alepetri/trap_camera/CAD/Pi/raspberry_pi_B+_(audio_video2).SLDPRT

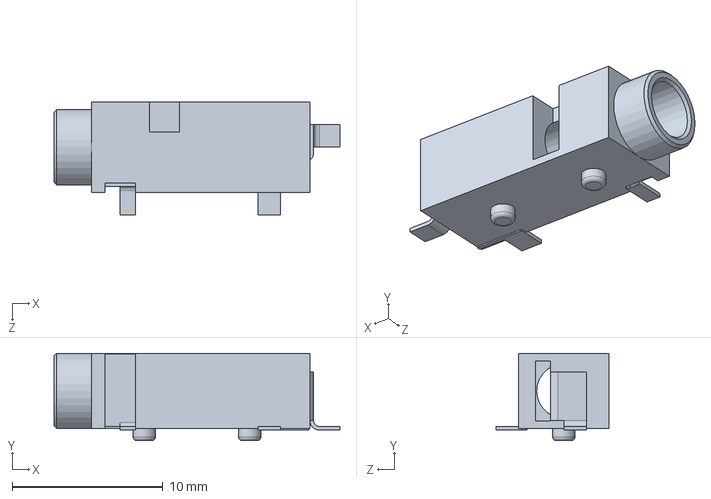
[picture p16: CAD file, 2021-12-30]
CAD/Pi/raspberry_pi_B+_(audio_video2).SLDPRT
19.0 x 5.80 x 7.50 mm
