alepetri/trap_camera/CAD/Trap_Camera_Lid.SLDPRT

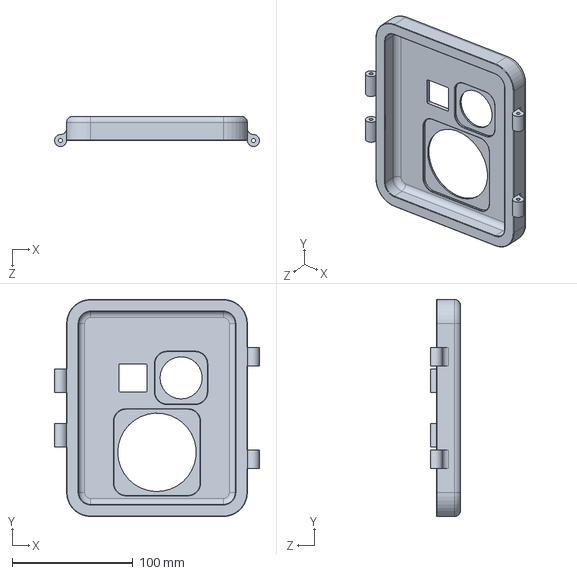
[picture p17: CAD file, 2021-12-30]
CAD/Trap_Camera_Lid.SLDPRT
170.0 x 180.0 x 25.0 mm
