alepetri/trap_camera/CAD/Pi/raspberry_pi_B+_(micro_USB_cover).SLDPRT

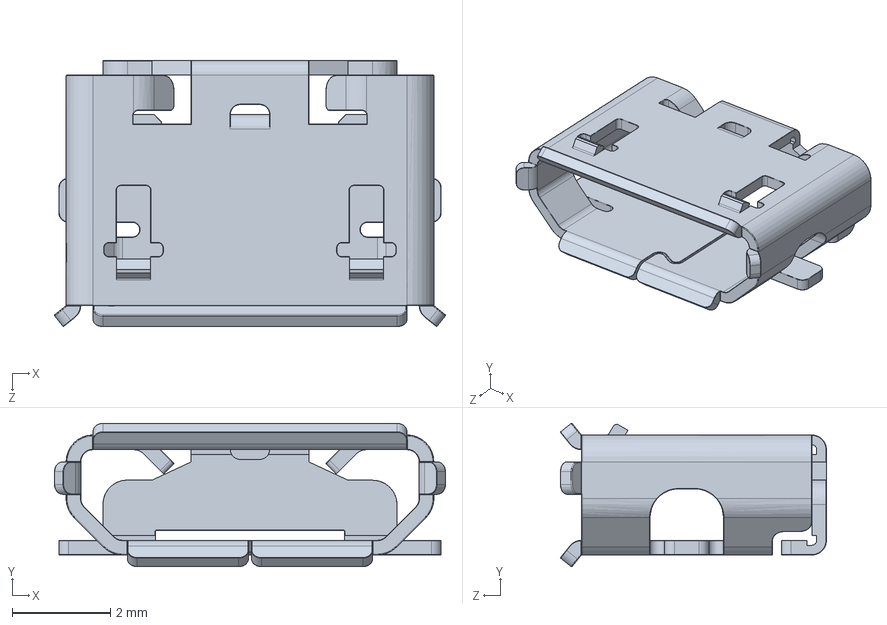
[picture p18: CAD file, 2021-12-30]
CAD/Pi/raspberry_pi_B+_(micro_USB_cover).SLDPRT
7.97 x 2.92 x 5.43 mm
