alepetri/trap_camera/CAD/test.STL

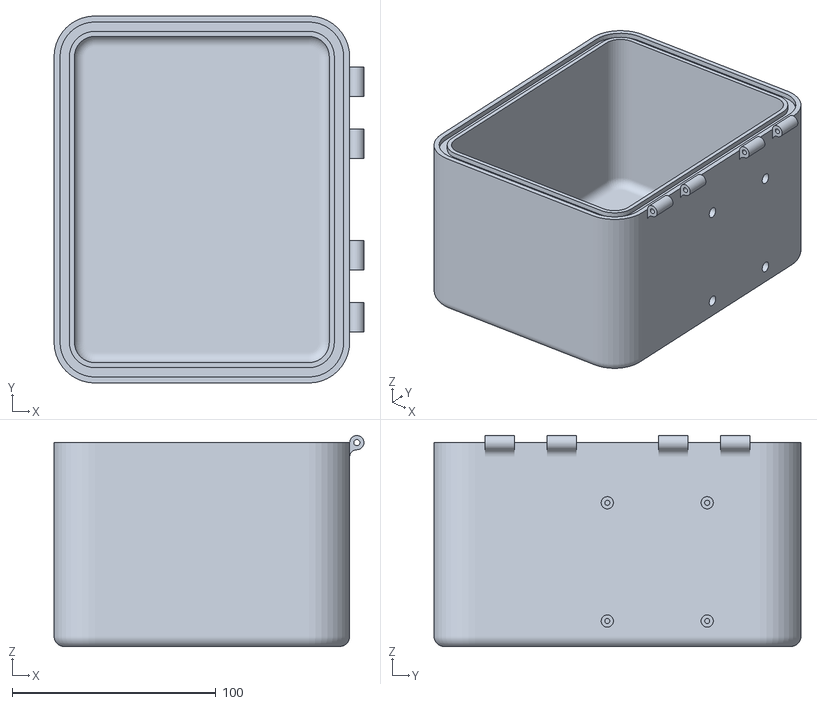
[picture p19: CAD file, 2021-12-30]
CAD/test.STL
152.0 x 180.0 x 103.5
