alepetri/trap_camera/CAD/Pi/raspberry_pi_B+_(microsd_slot2).SLDPRT

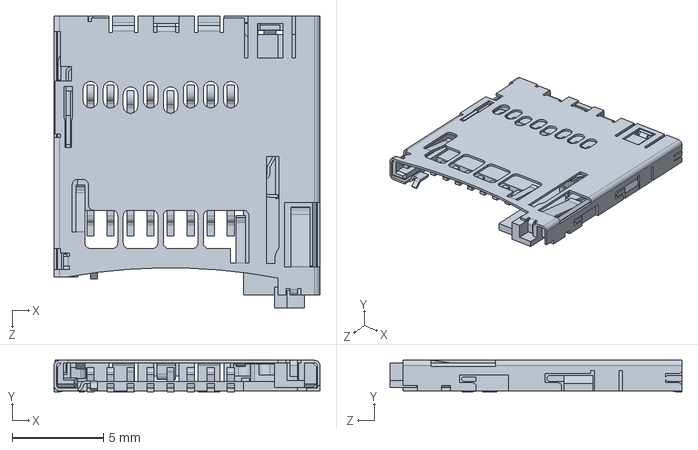
[picture p20: CAD file, 2021-12-30]
CAD/Pi/raspberry_pi_B+_(microsd_slot2).SLDPRT
14.6 x 1.73 x 16.0 mm
