alepetri/trap_camera/CAD/Pi/raspberry_pi__15_pin_FFC_Connector_locker.SLDPRT

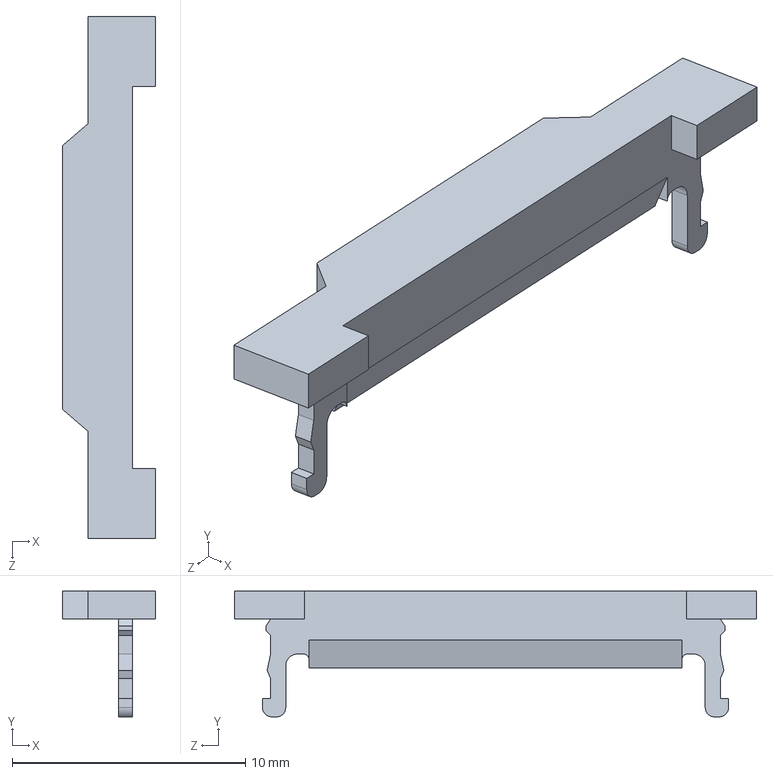
[picture p22: CAD file, 2021-12-30]
CAD/Pi/raspberry_pi__15_pin_FFC_Connector_locker.SLDPRT
4.00 x 5.40 x 22.4 mm
