alepetri/trap_camera/CAD/test_fitting.SLDPRT

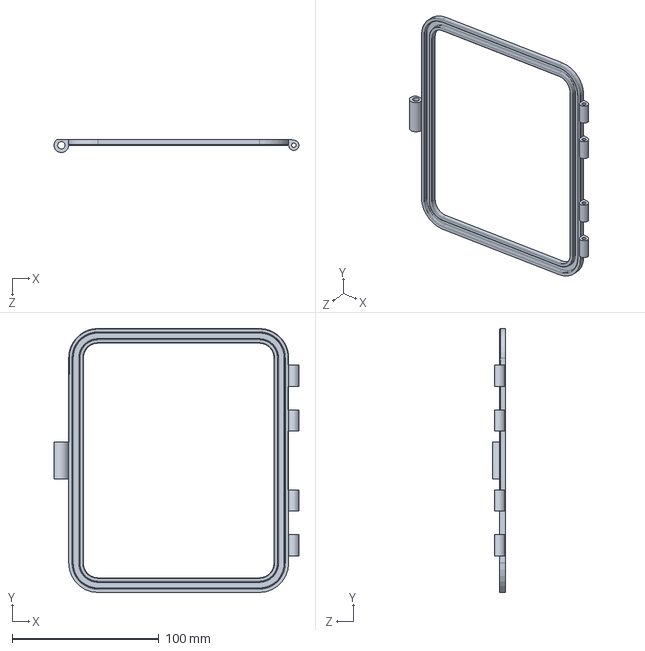
[picture p23: CAD file, 2021-12-30]
CAD/test_fitting.SLDPRT
167.0 x 180.0 x 8.99 mm
