alepetri/trap_camera/CAD/Pi/raspberry_pi__HDMI_socket_large_pin.SLDPRT

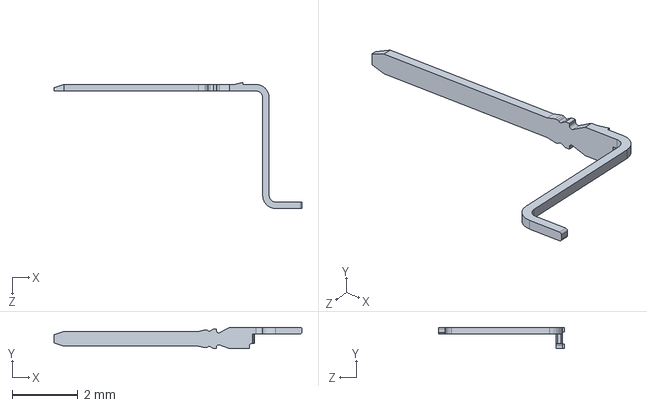
[picture p24: CAD file, 2021-12-30]
CAD/Pi/raspberry_pi__HDMI_socket_large_pin.SLDPRT
7.55 x 0.65 x 3.84 mm
