alepetri/trap_camera/CAD/Pi/raspberry_pi_B+_(CI_Board).SLDPRT

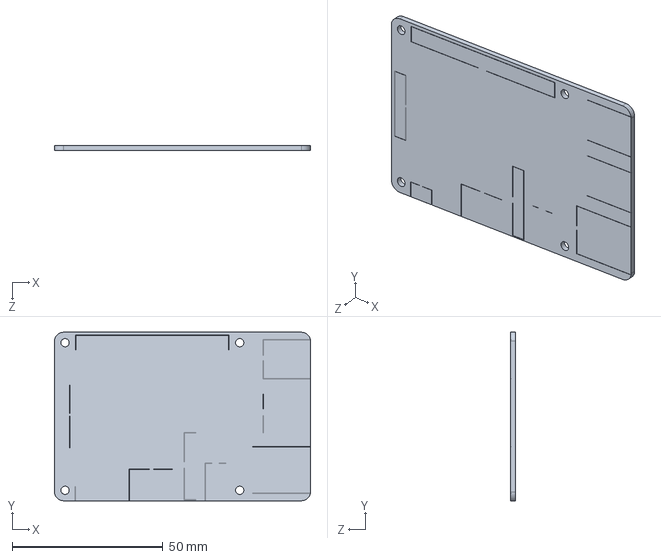
[picture p25: CAD file, 2021-12-30]
CAD/Pi/raspberry_pi_B+_(CI_Board).SLDPRT
85.0 x 56.0 x 1.60 mm
