alepetri/trap_camera/CAD/Pi/raspberry_pi__15_pin_FFC_Connector_pins.SLDPRT

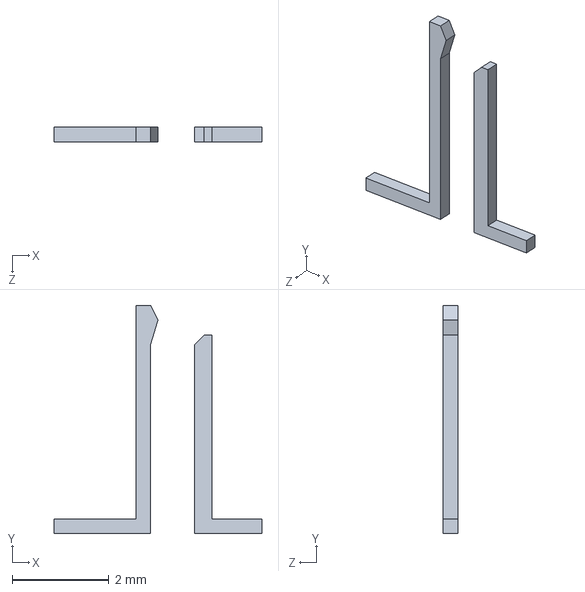
[picture p26: CAD file, 2021-12-30]
CAD/Pi/raspberry_pi__15_pin_FFC_Connector_pins.SLDPRT
4.30 x 4.71 x 0.3 mm
