alepetri/trap_camera/CAD/Pi/raspberry_pi_B+_(USB_x2_part1).SLDPRT

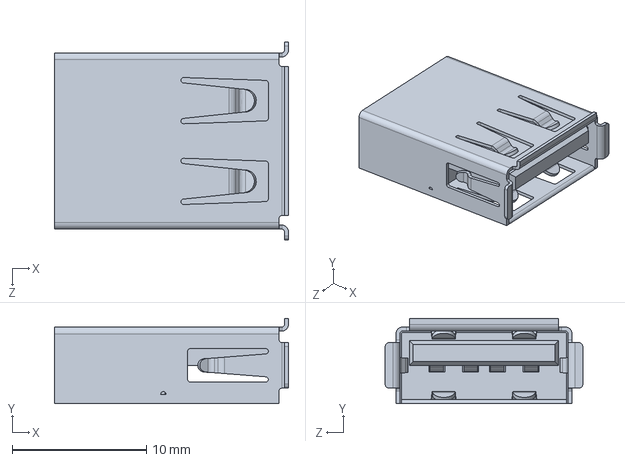
[picture p27: CAD file, 2021-12-30]
CAD/Pi/raspberry_pi_B+_(USB_x2_part1).SLDPRT
17.4 x 6.35 x 14.7 mm
