alepetri/trap_camera/CAD/SMAKN_12v_5v_DC_Converter.SLDPRT

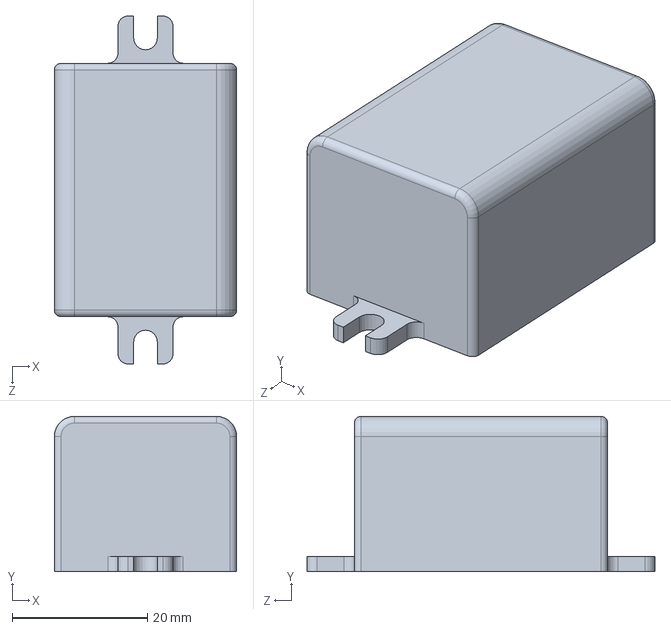
[picture p28: CAD file, 2021-12-30]
CAD/SMAKN_12v_5v_DC_Converter.SLDPRT
27.0 x 23.0 x 51.5 mm
