alepetri/trap_camera/CAD/base_hole_test.SLDPRT

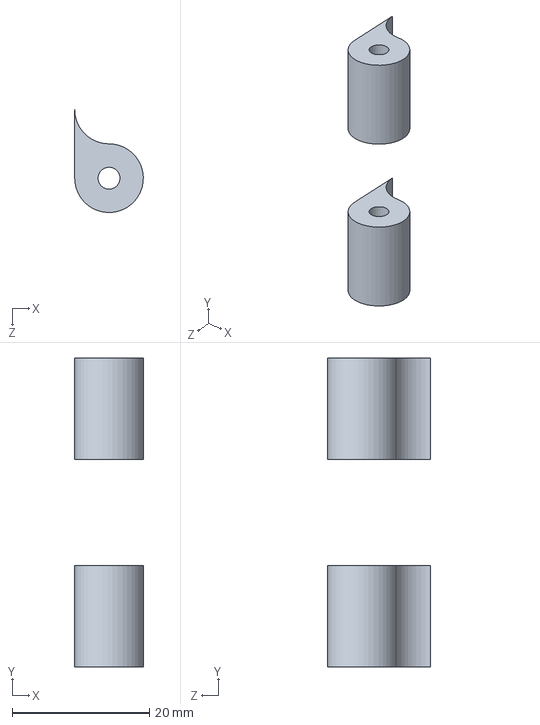
[picture p29: CAD file, 2021-12-30]
CAD/base_hole_test.SLDPRT
9.99 x 45.0 x 15.0 mm
