alepetri/trap_camera/CAD/Pi/raspberry_pi_B+_(microsd2).SLDPRT

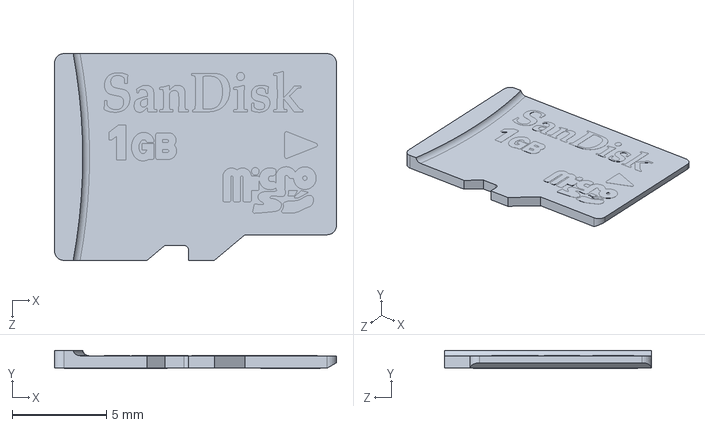
[picture p30: CAD file, 2021-12-30]
CAD/Pi/raspberry_pi_B+_(microsd2).SLDPRT
15.0 x 0.975 x 11.0 mm
