alepetri/trap_camera/CAD/illuminator_mount.SLDPRT

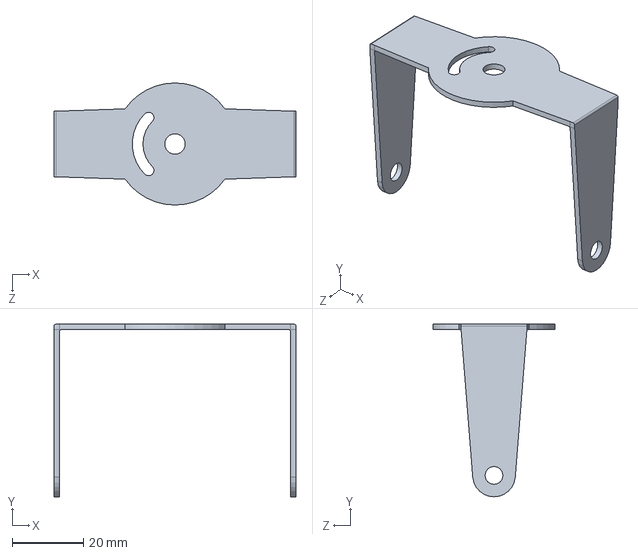
[picture p31: CAD file, 2021-12-30]
CAD/illuminator_mount.SLDPRT
68.0 x 48.5 x 34.3 mm
