alepetri/trap_camera/CAD/Pi/raspberry_pi__HDMI_socket_cover.SLDPRT

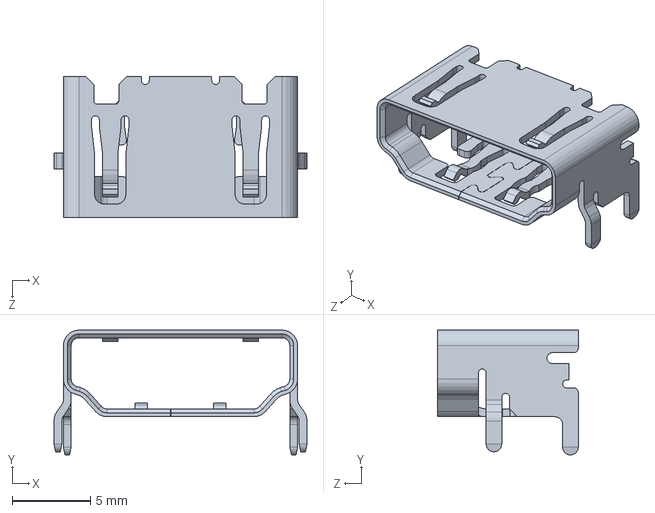
[picture p32: CAD file, 2021-12-30]
CAD/Pi/raspberry_pi__HDMI_socket_cover.SLDPRT
16.2 x 8.00 x 9.00 mm
