alepetri/trap_camera/CAD/camera_cover.SLDPRT

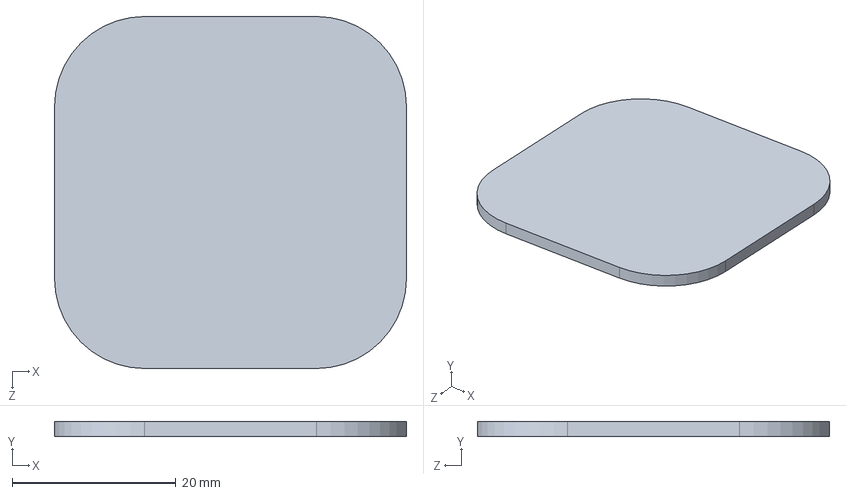
[picture p33: CAD file, 2021-12-30]
CAD/camera_cover.SLDPRT
43.0 x 1.80 x 43.0 mm
