alepetri/trap_camera/CAD/Pi/raspberry_pi_B+_(USB_x2_part2).SLDPRT

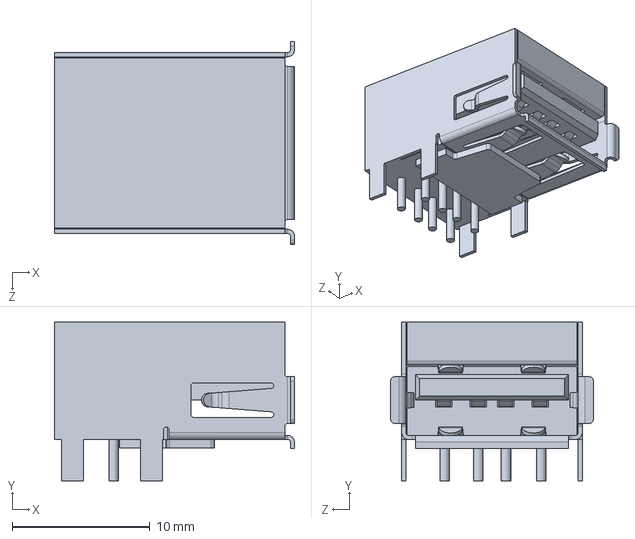
[picture p34: CAD file, 2021-12-30]
CAD/Pi/raspberry_pi_B+_(USB_x2_part2).SLDPRT
17.4 x 11.5 x 14.7 mm
