alepetri/trap_camera/CAD/Pi/raspberry_pi__HDMI_socket_small_pin.SLDPRT

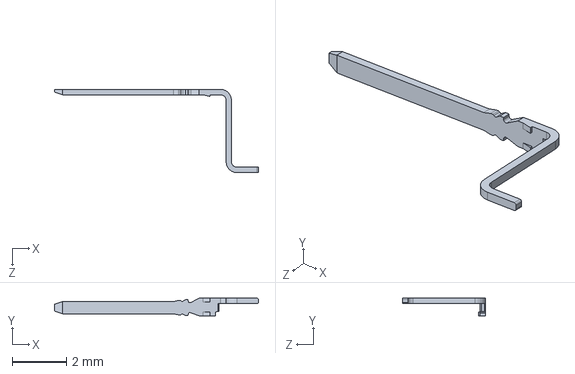
[picture p35: CAD file, 2021-12-30]
CAD/Pi/raspberry_pi__HDMI_socket_small_pin.SLDPRT
7.55 x 0.65 x 3.08 mm
