alepetri/trap_camera/CAD/illuminator_cover.SLDPRT

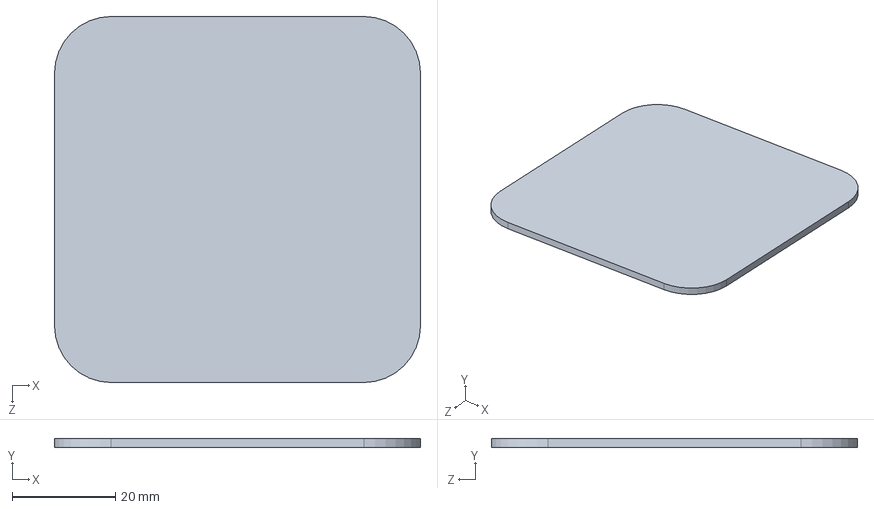
[picture p36: CAD file, 2021-12-30]
CAD/illuminator_cover.SLDPRT
71.0 x 1.80 x 71.0 mm
