alepetri/trap_camera/CAD/IR_Illuminator.SLDPRT

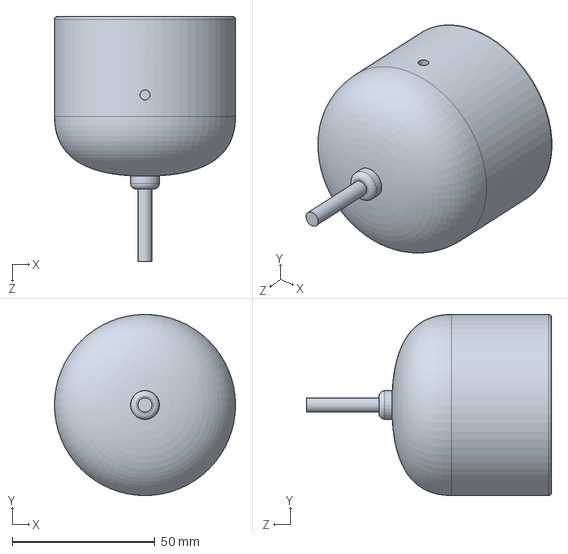
[picture p37: CAD file, 2021-12-30]
CAD/IR_Illuminator.SLDPRT
63.5 x 63.5 x 85.9 mm
