alepetri/trap_camera/CAD/Pi/raspberry_pi_B+_(QFN64).SLDPRT

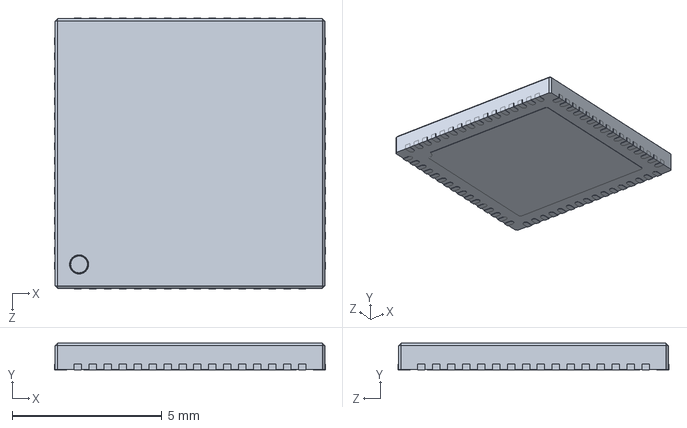
[picture p38: CAD file, 2021-12-30]
CAD/Pi/raspberry_pi_B+_(QFN64).SLDPRT
9.04 x 0.9 x 9.04 mm
