alepetri/trap_camera/CAD/Battery.SLDPRT

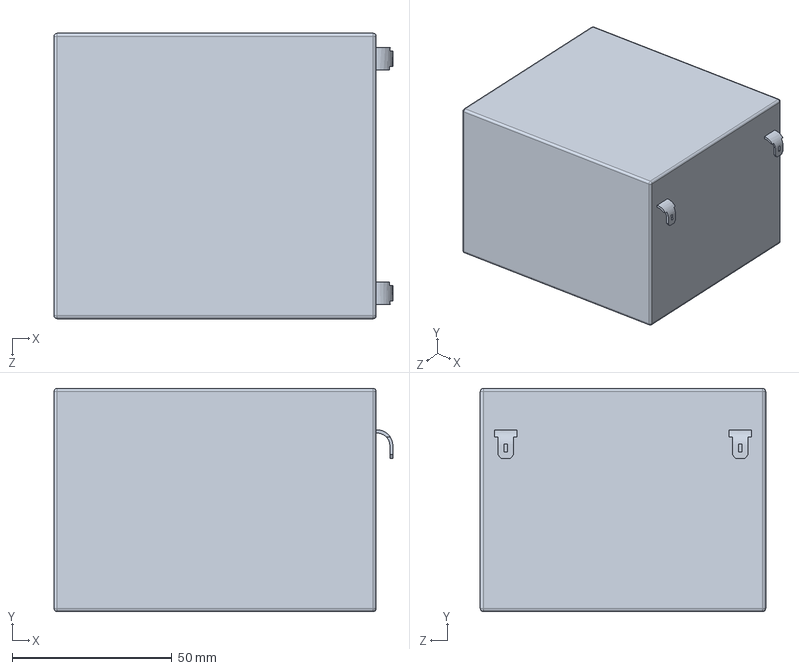
[picture p39: CAD file, 2021-12-30]
CAD/Battery.SLDPRT
106.2 x 70.0 x 89.5 mm
