alepetri/trap_camera/CAD/Pi/raspberry_pi__HDMI_socket_inside.SLDPRT

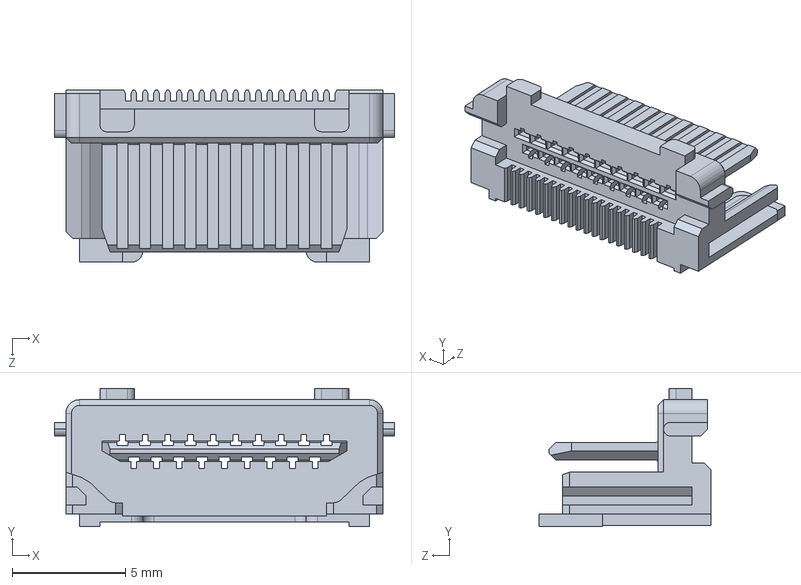
[picture p40: CAD file, 2021-12-30]
CAD/Pi/raspberry_pi__HDMI_socket_inside.SLDPRT
15.0 x 6.10 x 7.60 mm
