alepetri/trap_camera/CAD/Pi/raspberry_pi_B+_(bar_180_2x20).SLDPRT

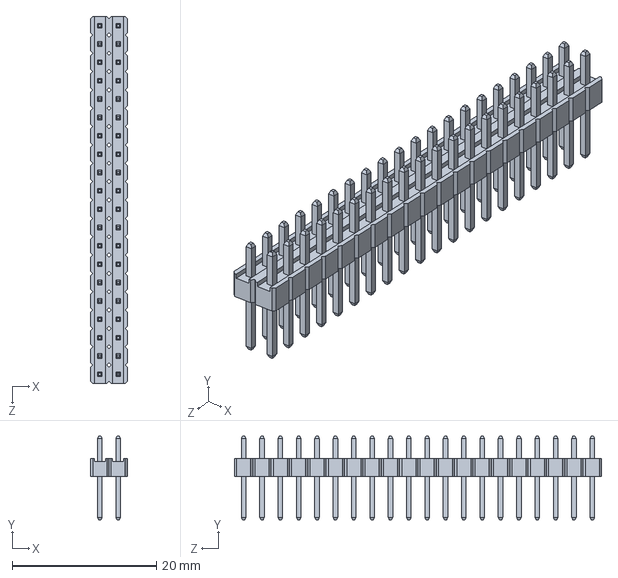
[picture p41: CAD file, 2021-12-30]
CAD/Pi/raspberry_pi_B+_(bar_180_2x20).SLDPRT
5.08 x 11.6 x 50.8 mm
