alepetri/trap_camera/CAD/Trap_Camera_Base.SLDPRT

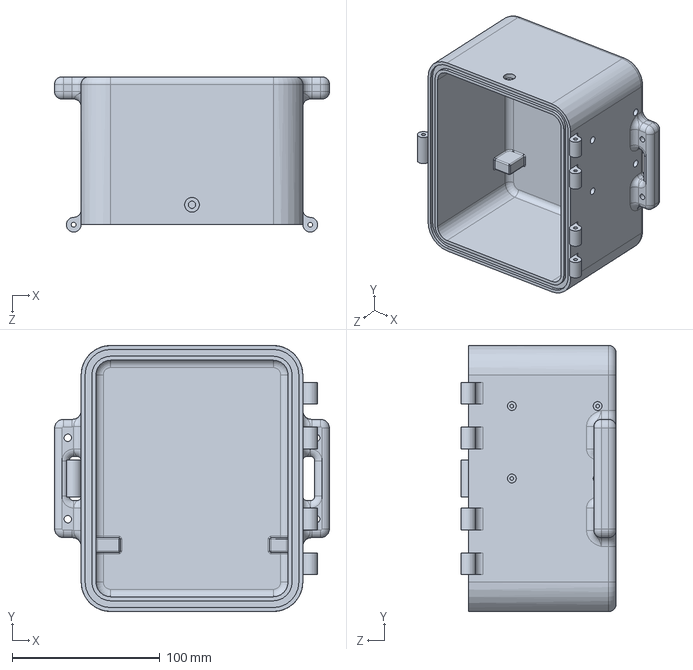
[picture p42: CAD file, 2021-12-30]
CAD/Trap_Camera_Base.SLDPRT
186.0 x 180.0 x 105.0 mm
