alepetri/trap_camera/CAD/cam_mount.SLDPRT

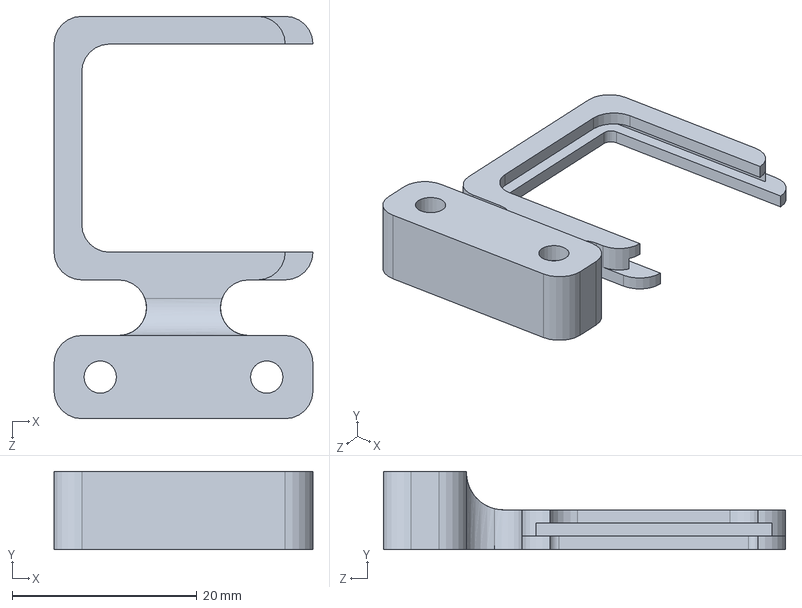
[picture p43: CAD file, 2021-12-30]
CAD/cam_mount.SLDPRT
28.0 x 8.45 x 43.5 mm
