alepetri/trap_camera/CAD/Pi/raspberry_pi_B+_(168_FBGA_12x12).SLDPRT

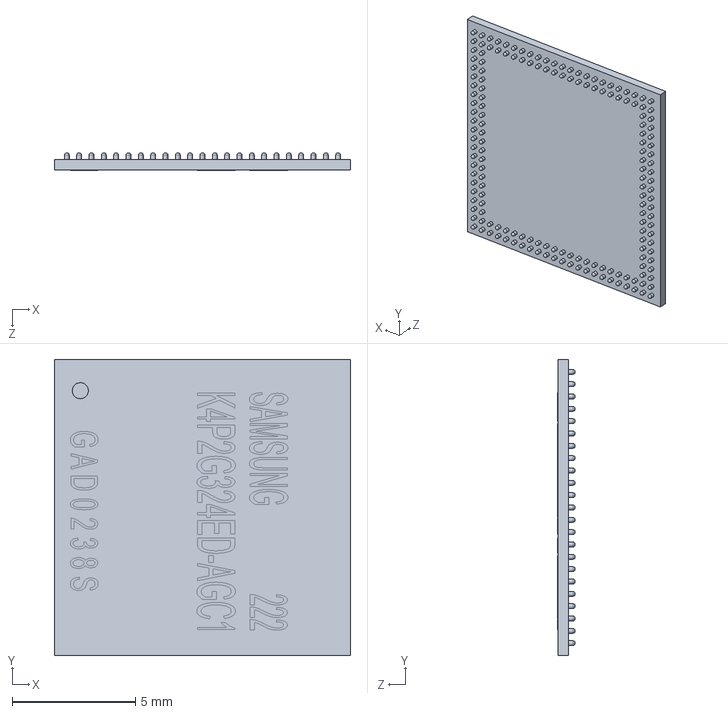
[picture p44: CAD file, 2021-12-30]
CAD/Pi/raspberry_pi_B+_(168_FBGA_12x12).SLDPRT
12.0 x 12.0 x 0.71 mm
