alepetri/trap_camera/CAD/sensor.SLDPRT

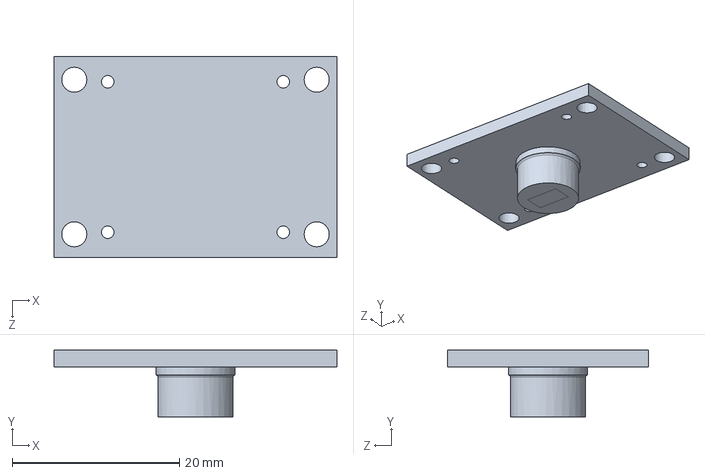
[picture p45: CAD file, 2021-12-30]
CAD/sensor.SLDPRT
33.9 x 8.00 x 24.0 mm
