alepetri/trap_camera/CAD/Pi/raspberry_pi__15_pin_FFC_Connector_body.SLDPRT

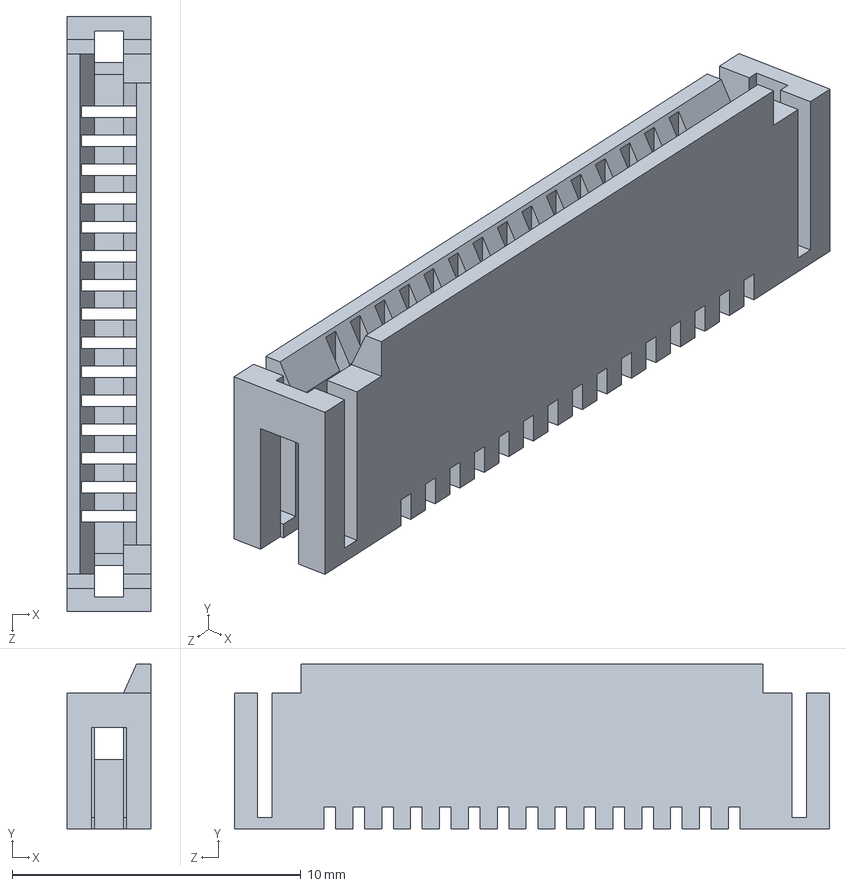
[picture p46: CAD file, 2021-12-30]
CAD/Pi/raspberry_pi__15_pin_FFC_Connector_body.SLDPRT
2.90 x 5.70 x 20.6 mm
