alepetri/trap_camera/CAD/test2.STL

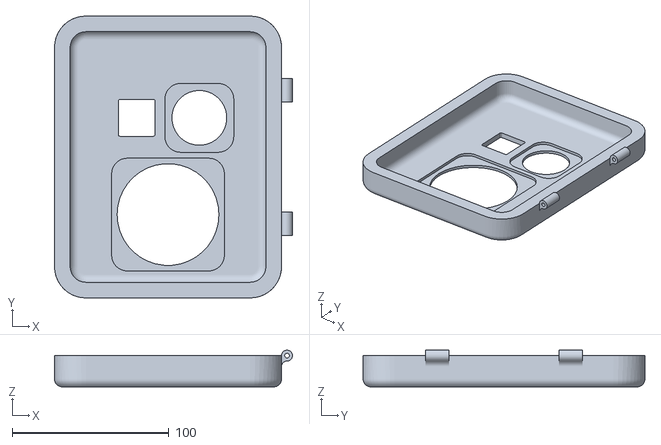
[picture p47: CAD file, 2021-12-30]
CAD/test2.STL
152.0 x 180.0 x 23.5
